Jartza/PS2toAmiga/inc/convert_table.h

/*
 * PS2 to Amiga keyboard converter for ATTiny85.
 * 
 * Translation table from PS2KeyAdvanced codes to Amiga keycodes. Stored in RAM
 * for faster access.
 * 
 * (C) 2022 by Jari Tulilahti. Licensed under LGPL, see LICENSE for more info.
 */
#pragma once

// Table to convert from PS2KeyAdvanced to Amiga keycode. 0xFF = Don't send anything
const uint8_t ps2amiga[256] =
{
    0xFF,    // 0x00
    0xFF,    // 0x01
    0xFF,    // 0x02
    0x62,    // 0x03
    0xFF,    // 0x04
    0xFF,    // 0x05
    0x60,    // 0x06
    0x61,    // 0x07
    0x63,    // 0x08
    0xFF,    // 0x09
    0x64,    // 0x0A
    0x65,    // 0x0B
    0x66,    // 0x0C
    0x67,    // 0x0D
    0x67,    // 0x0E
    0xFF,    // 0x0F
    0xFF,    // 0x10
    0x5F,    // 0x11
    0xFF,    // 0x12
    0xFF,    // 0x13
    0xFF,    // 0x14
    0x4F,    // 0x15
    0x4E,    // 0x16
    0x4C,    // 0x17
    0x4D,    // 0x18
    0xFF,    // 0x19
    0x46,    // 0x1A
    0x45,    // 0x1B
    0x41,    // 0x1C
    0x42,    // 0x1D
    0x44,    // 0x1E
    0x40,    // 0x1F
    0x0F,    // 0x20
    0x1D,    // 0x21
    0x1E,    // 0x22
    0x1F,    // 0x23
    0x2D,    // 0x24
    0x2E,    // 0x25
    0x2F,    // 0x26
    0x3D,    // 0x27
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
};
